gatgoutkouni-creator/Assistance-soudure-PCB/PFE kouni/decoupe laser/Pièce3.DXF

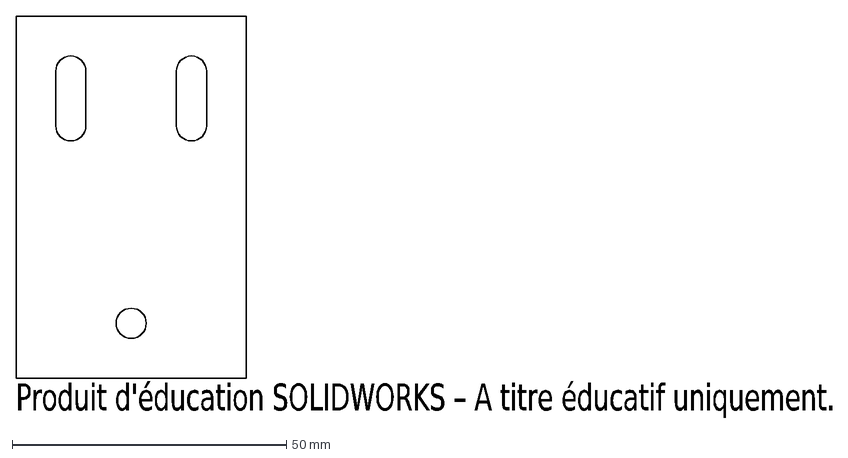
[picture p14: CAD file, 2026-09-05]
PFE kouni/decoupe laser/Pièce3.DXF
Produit d'éducation SOLIDWORKS – A titre éducatif uniquement.
