gatgoutkouni-creator/Assistance-soudure-PCB/PFE kouni/vis.SLDPRT

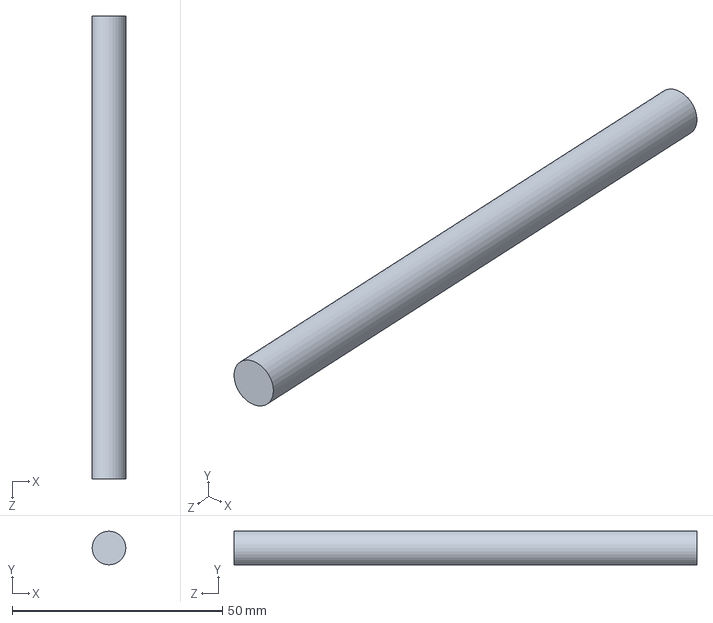
[picture p15: CAD file, 2026-09-05]
PFE kouni/vis.SLDPRT
8.00 x 8.00 x 110.0 mm
