gatgoutkouni-creator/Assistance-soudure-PCB/PFE kouni/decoupe laser/plaque v slot 2.DXF

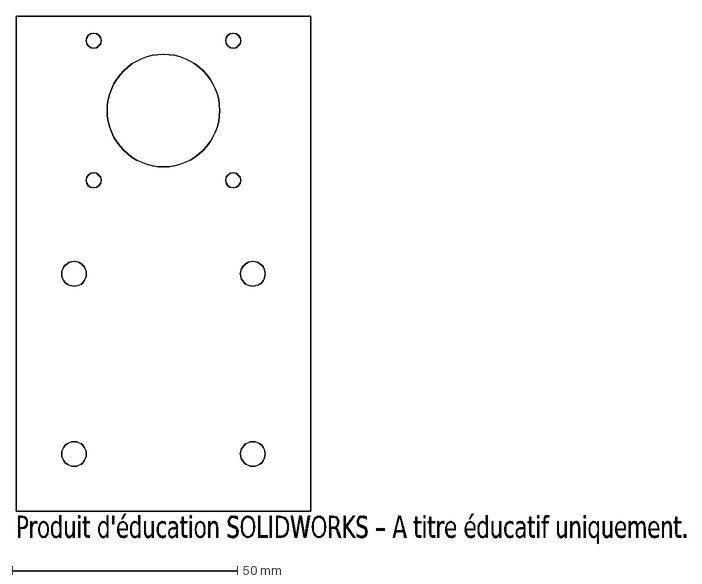
[picture p16: CAD file, 2026-09-05]
PFE kouni/decoupe laser/plaque v slot 2.DXF
Produit d'éducation SOLIDWORKS – A titre éducatif uniquement.
