gatgoutkouni-creator/Assistance-soudure-PCB/PFE kouni/fer/fer partie 2.SLDPRT

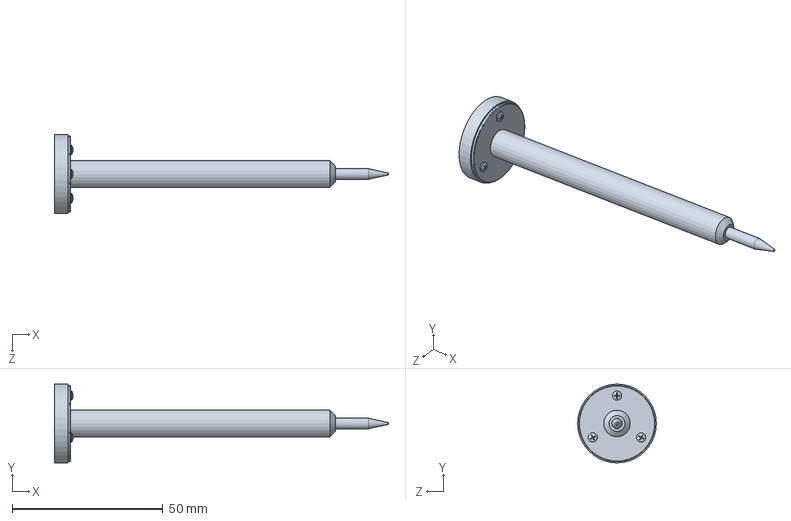
[picture p17: CAD file, 2026-09-05]
PFE kouni/fer/fer partie 2.SLDPRT
110.9 x 26.2 x 26.2 mm
