gatgoutkouni-creator/Assistance-soudure-PCB/PFE kouni/impression/Pièce3.STL

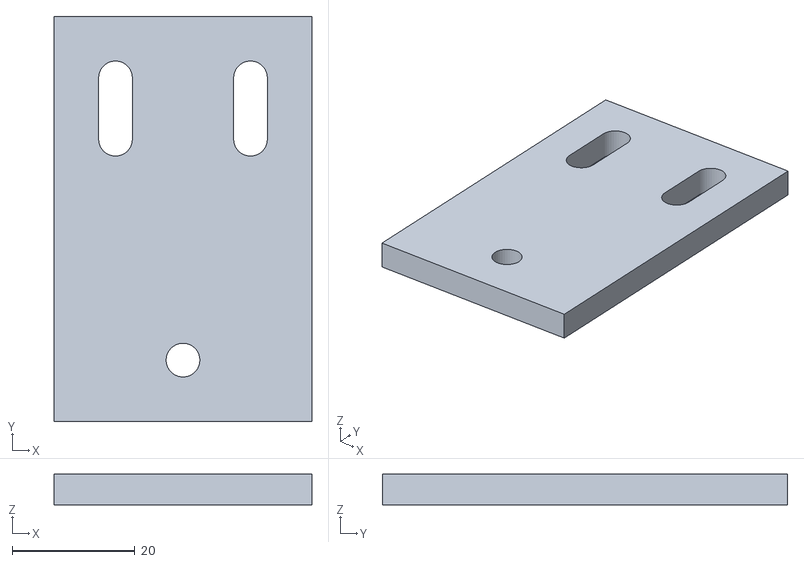
[picture p18: CAD file, 2026-09-05]
PFE kouni/impression/Pièce3.STL
42.0 x 66.0 x 5.00
