gatgoutkouni-creator/Assistance-soudure-PCB/PFE kouni/KOUNIII PIEECE 1 YTB.SLDPRT

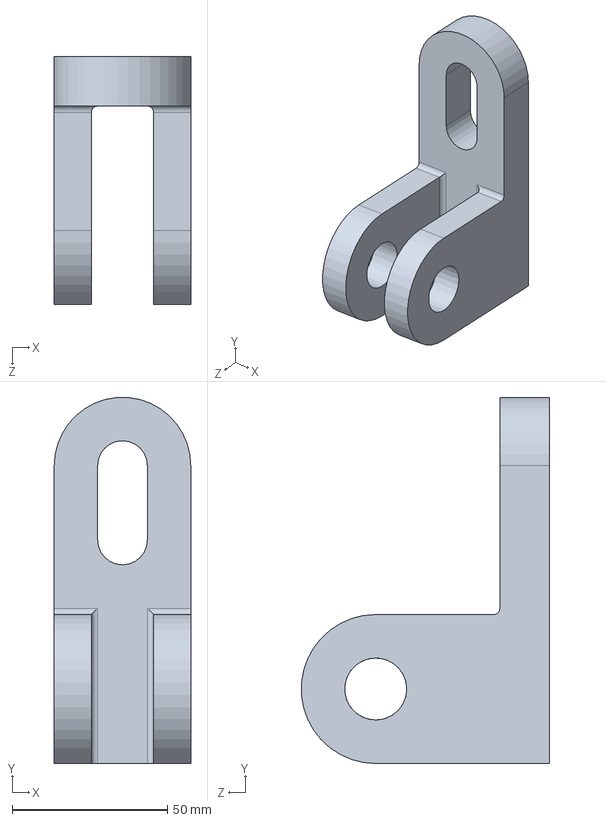
[picture p19: CAD file, 2026-09-05]
PFE kouni/KOUNIII PIEECE 1 YTB.SLDPRT
44.0 x 117.9 x 79.9 mm
