gatgoutkouni-creator/Assistance-soudure-PCB/PFE kouni/palier.SLDPRT

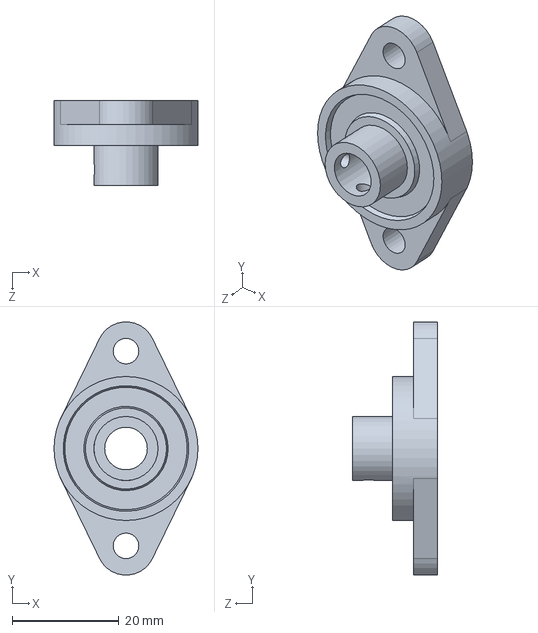
[picture p20: CAD file, 2026-09-05]
PFE kouni/palier.SLDPRT
27.0 x 47.4 x 16.0 mm
