gatgoutkouni-creator/Assistance-soudure-PCB/PFE kouni/courroie.SLDPRT

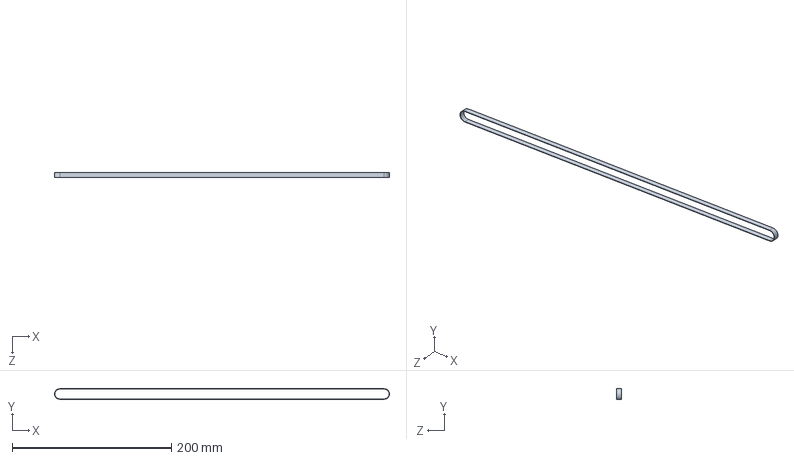
[picture p21: CAD file, 2026-09-05]
PFE kouni/courroie.SLDPRT
420.2 x 13.2 x 6.00 mm
