gatgoutkouni-creator/Assistance-soudure-PCB/PFE kouni/GHLIDH 2.SLDPRT

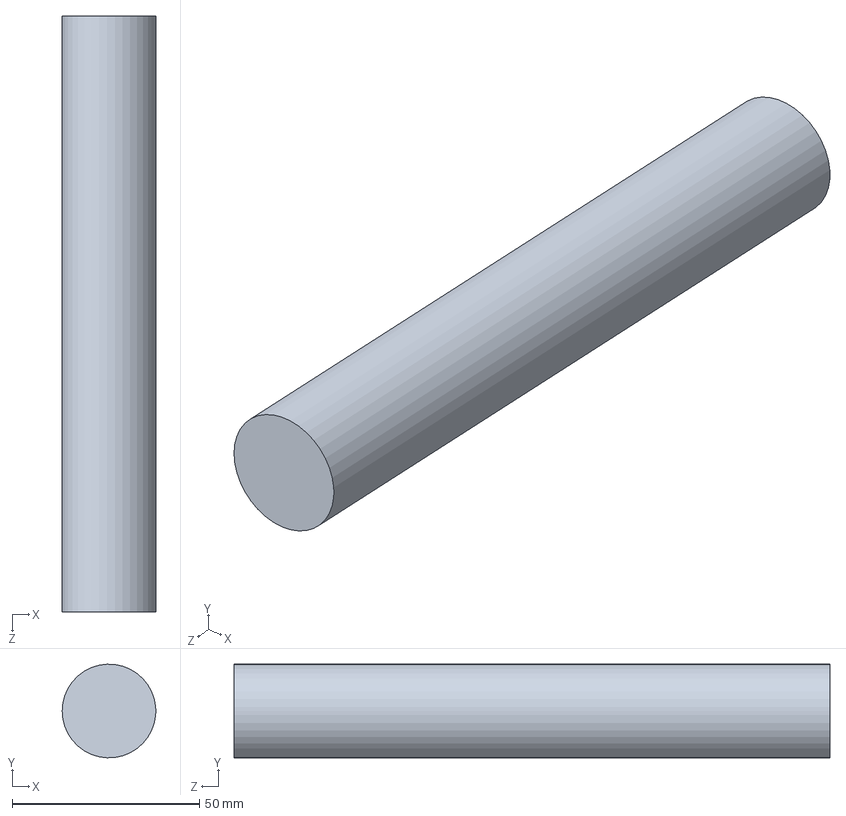
[picture p22: CAD file, 2026-09-05]
PFE kouni/GHLIDH 2.SLDPRT
25.0 x 25.0 x 159.0 mm
