gatgoutkouni-creator/Assistance-soudure-PCB/PFE kouni/plaque axe z.SLDPRT

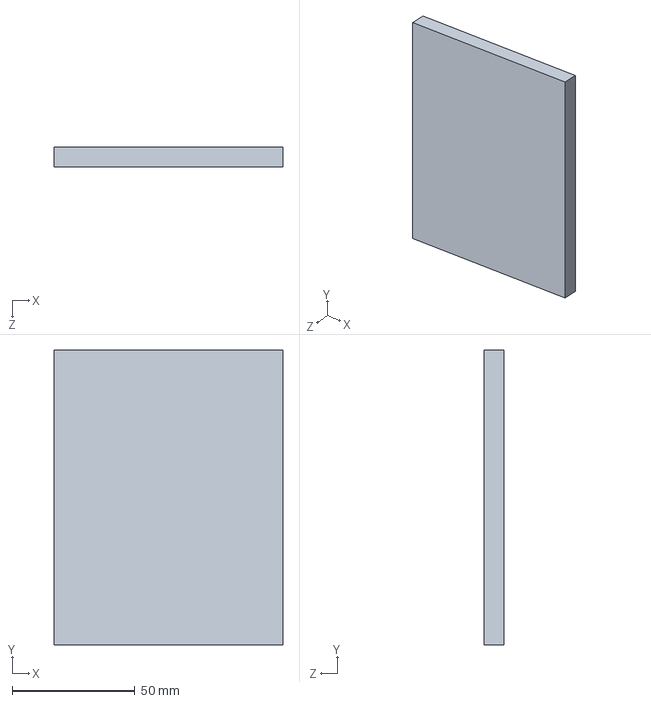
[picture p23: CAD file, 2026-09-05]
PFE kouni/plaque axe z.SLDPRT
93.0 x 120.0 x 8.00 mm
