gatgoutkouni-creator/Assistance-soudure-PCB/PFE kouni/Pièce2 YTB.SLDPRT

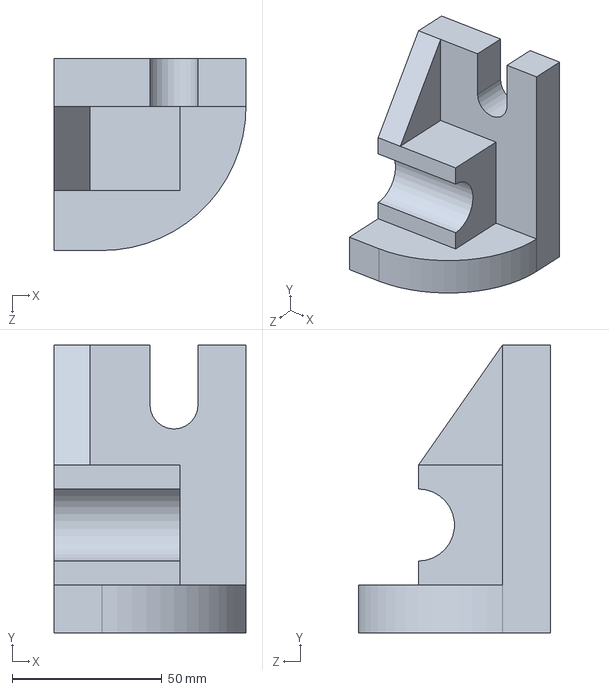
[picture p24: CAD file, 2026-09-05]
PFE kouni/Pièce2 YTB.SLDPRT
64.0 x 96.0 x 64.0 mm
