gatgoutkouni-creator/Assistance-soudure-PCB/PFE kouni/guidage z.SLDPRT

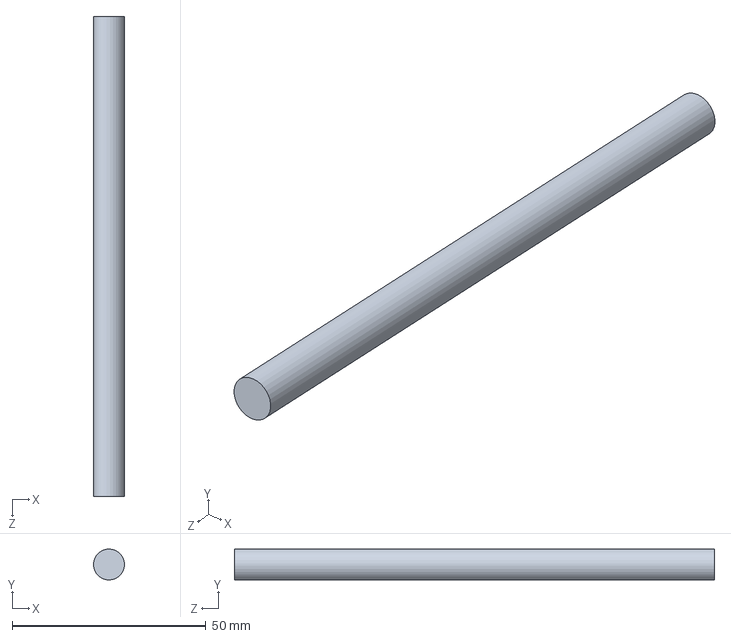
[picture p25: CAD file, 2026-09-05]
PFE kouni/guidage z.SLDPRT
8.00 x 7.99 x 124.0 mm
