gatgoutkouni-creator/Assistance-soudure-PCB/PFE kouni/v-slot X2.SLDPRT

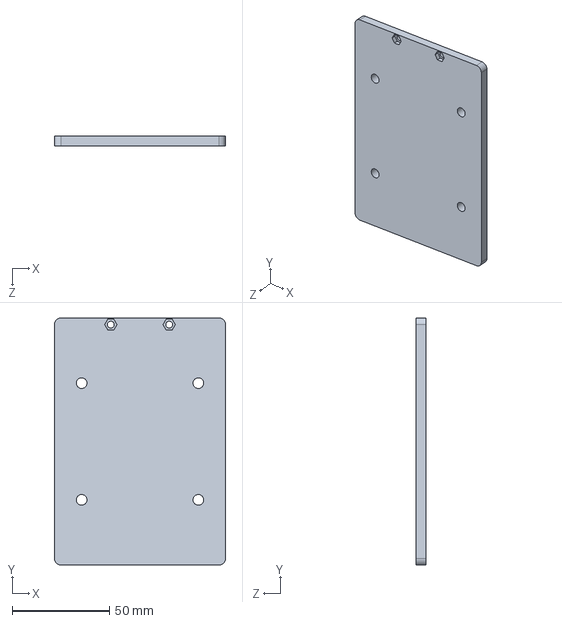
[picture p26: CAD file, 2026-09-05]
PFE kouni/v-slot X2.SLDPRT
88.0 x 127.0 x 5.00 mm
