gatgoutkouni-creator/Assistance-soudure-PCB/PFE kouni/42SHD0034-20B.SLDPRT

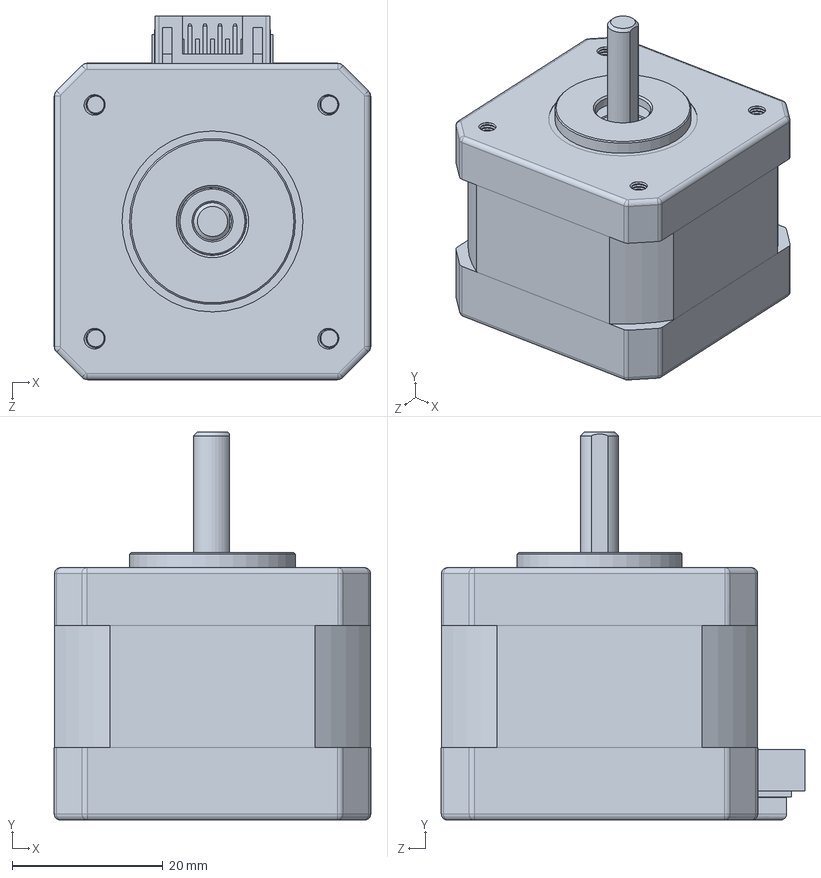
[picture p27: CAD file, 2026-09-05]
PFE kouni/42SHD0034-20B.SLDPRT
42.0 x 51.5 x 48.2 mm
