gatgoutkouni-creator/Assistance-soudure-PCB/PFE kouni/3030 ALUMINIUM EXTRUSION.SLDPRT

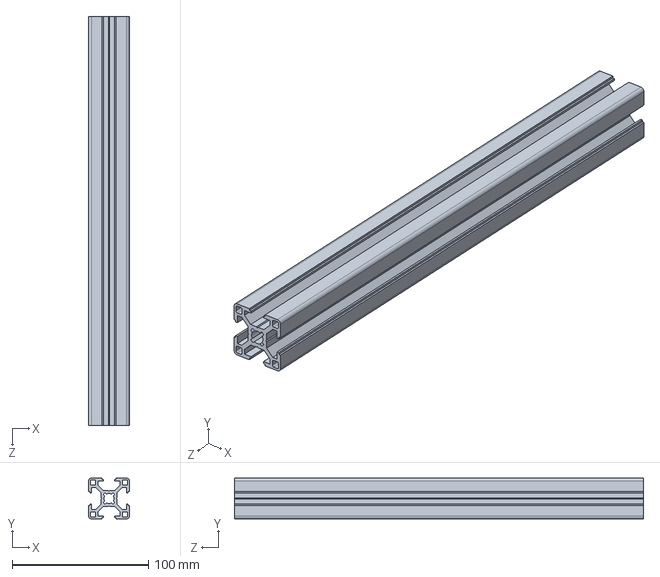
[picture p28: CAD file, 2026-09-05]
PFE kouni/3030 ALUMINIUM EXTRUSION.SLDPRT
30.0 x 30.0 x 300.0 mm
