gatgoutkouni-creator/Assistance-soudure-PCB/PFE kouni/roulement lineaire.SLDPRT

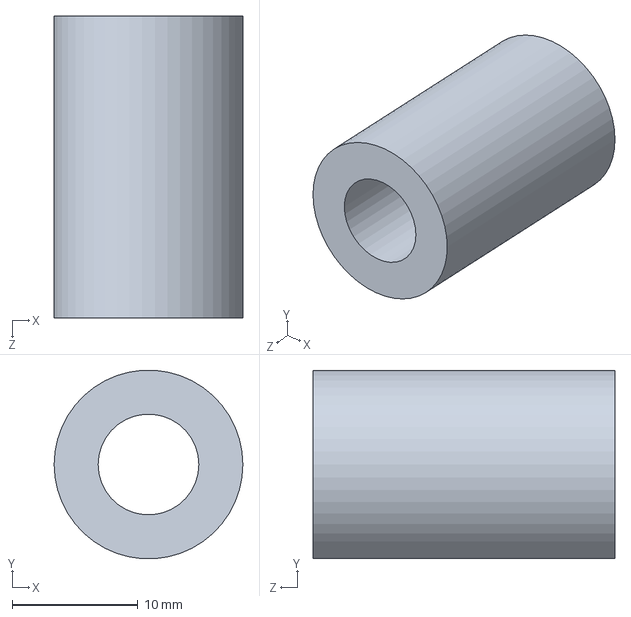
[picture p29: CAD file, 2026-09-05]
PFE kouni/roulement lineaire.SLDPRT
15.0 x 15.0 x 24.0 mm
