gatgoutkouni-creator/Assistance-soudure-PCB/PFE kouni/obs courroie.SLDPRT

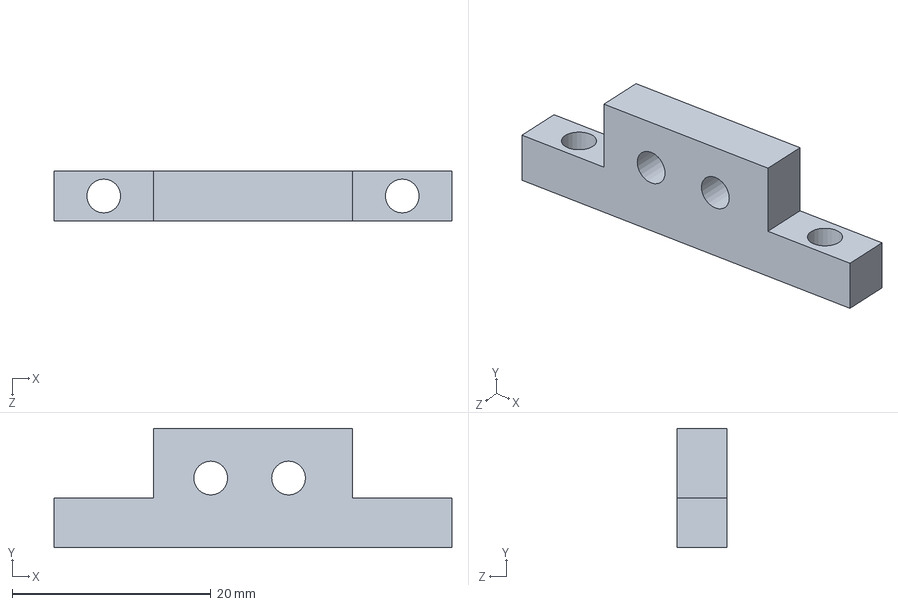
[picture p30: CAD file, 2026-09-05]
PFE kouni/obs courroie.SLDPRT
40.0 x 12.0 x 5.00 mm
