gatgoutkouni-creator/Assistance-soudure-PCB/PFE kouni/cphg19-5-8_01.SLDPRT

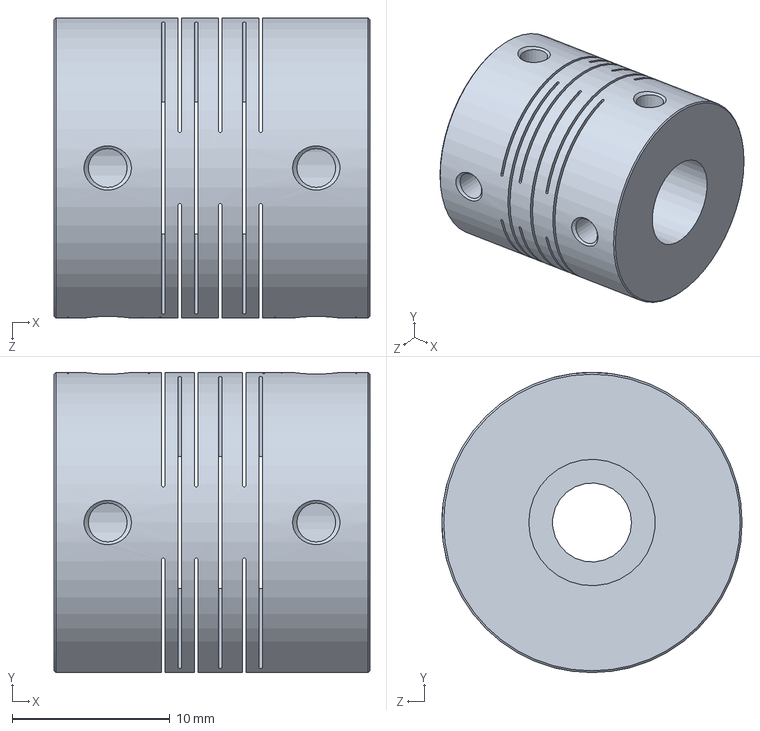
[picture p31: CAD file, 2026-09-05]
PFE kouni/cphg19-5-8_01.SLDPRT
20.0 x 19.0 x 19.0 mm
