gatgoutkouni-creator/Assistance-soudure-PCB/PFE kouni/GHLIDH.SLDPRT

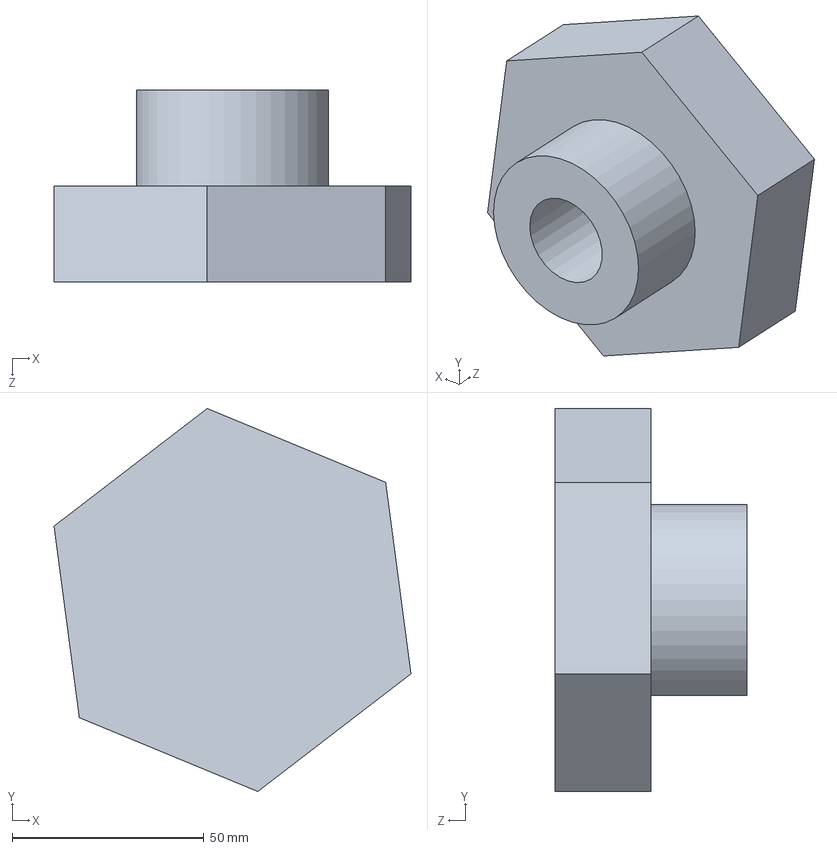
[picture p32: CAD file, 2026-09-05]
PFE kouni/GHLIDH.SLDPRT
93.2 x 100.0 x 50.0 mm
