gatgoutkouni-creator/Assistance-soudure-PCB/PFE kouni/pas a pas etain.SLDPRT

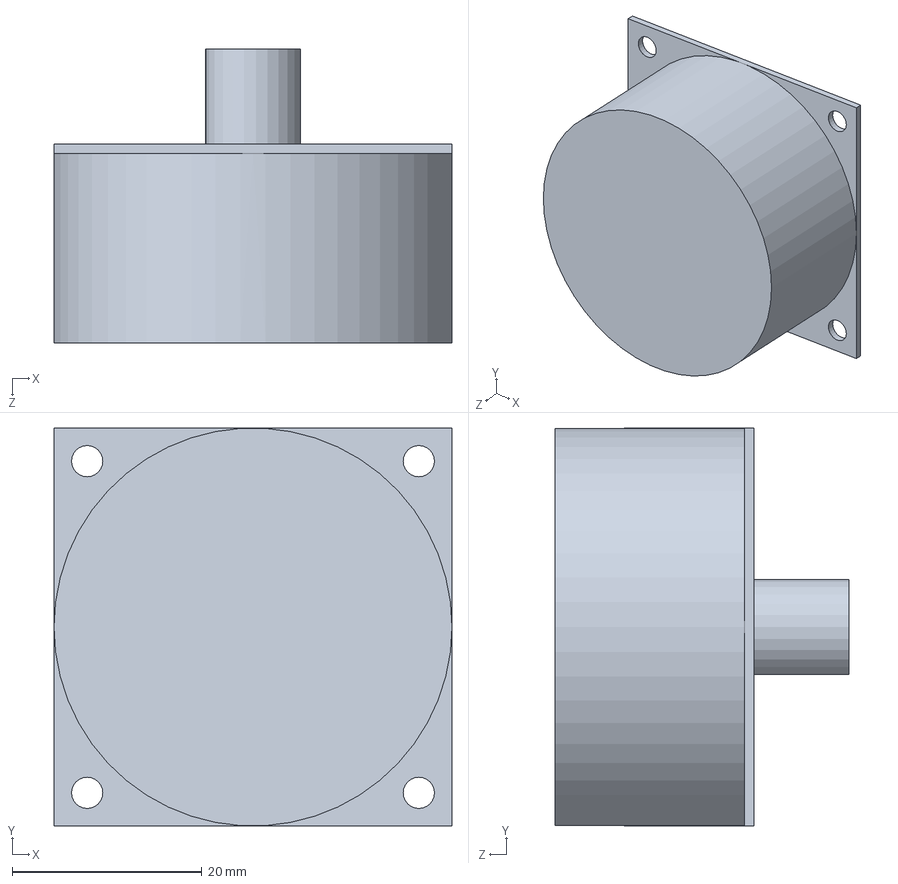
[picture p33: CAD file, 2026-09-05]
PFE kouni/pas a pas etain.SLDPRT
42.0 x 42.0 x 31.0 mm
