gatgoutkouni-creator/Assistance-soudure-PCB/PFE kouni/table.SLDPRT

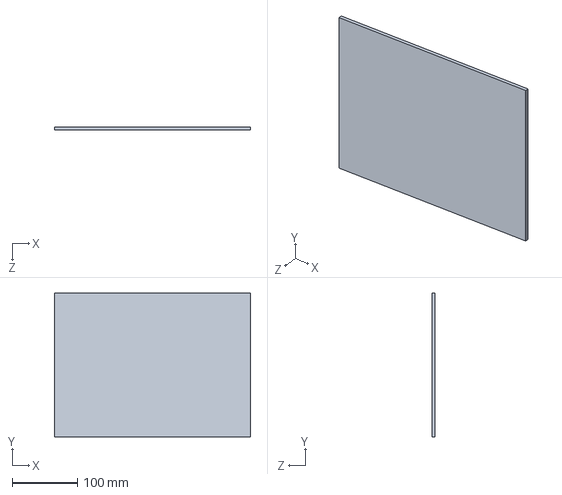
[picture p34: CAD file, 2026-09-05]
PFE kouni/table.SLDPRT
300.0 x 220.0 x 5.00 mm
