gatgoutkouni-creator/Assistance-soudure-PCB/PFE kouni/support etain.SLDPRT

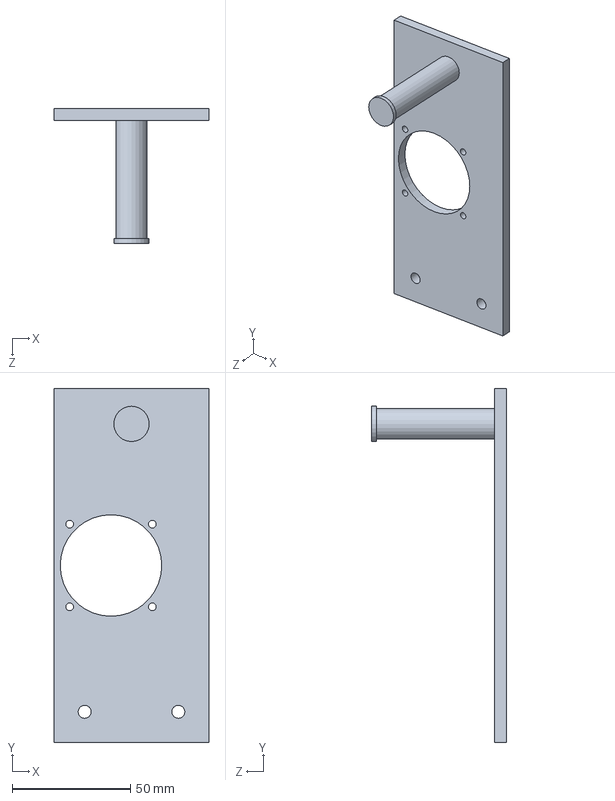
[picture p35: CAD file, 2026-09-05]
PFE kouni/support etain.SLDPRT
65.5 x 150.0 x 57.0 mm
