gatgoutkouni-creator/Assistance-soudure-PCB/PFE kouni/GT2 x 6mm Pully 5mm Bore syncro.SLDPRT

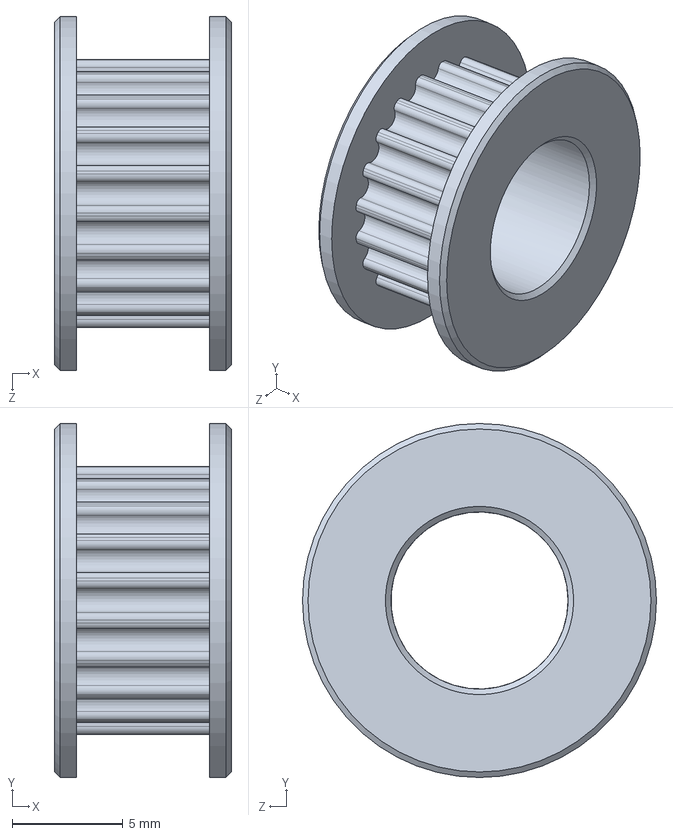
[picture p36: CAD file, 2026-09-05]
PFE kouni/GT2 x 6mm Pully 5mm Bore syncro.SLDPRT
8.00 x 16.0 x 16.0 mm
