gatgoutkouni-creator/Assistance-soudure-PCB/PFE kouni/Aluminum Profile 2040.SLDPRT

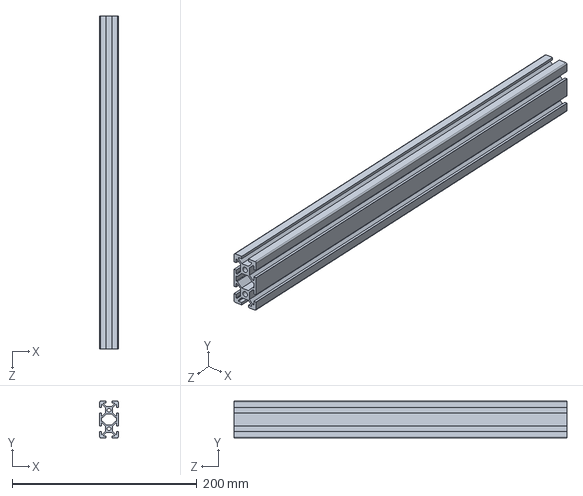
[picture p37: CAD file, 2026-09-05]
PFE kouni/Aluminum Profile 2040.SLDPRT
20.0 x 40.0 x 360.0 mm
