gatgoutkouni-creator/Assistance-soudure-PCB/PFE kouni/support ecrou.SLDPRT

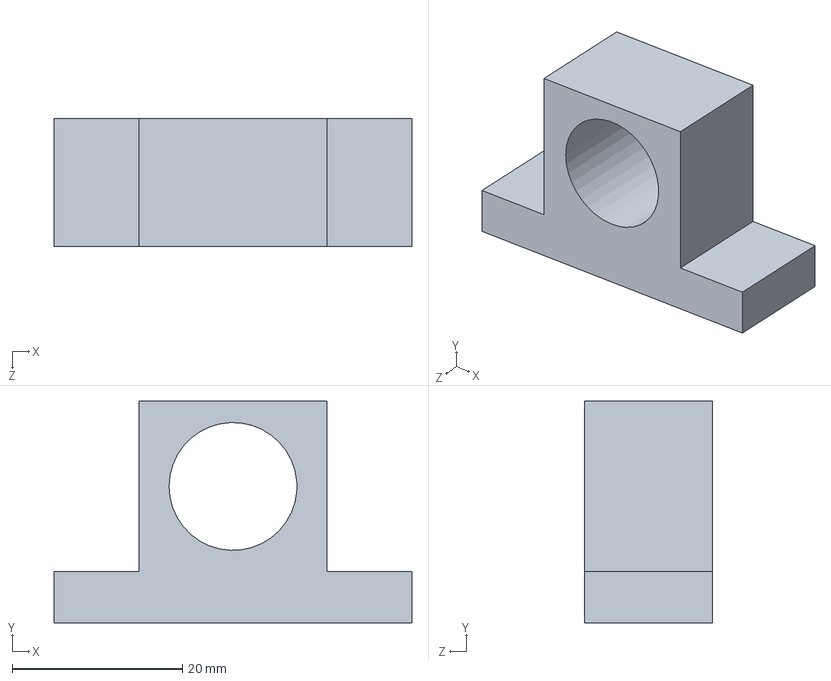
[picture p38: CAD file, 2026-09-05]
PFE kouni/support ecrou.SLDPRT
42.0 x 26.0 x 15.0 mm
