gatgoutkouni-creator/Assistance-soudure-PCB/PFE kouni/2020 ALUMINIUM EXTRUSION.SLDPRT

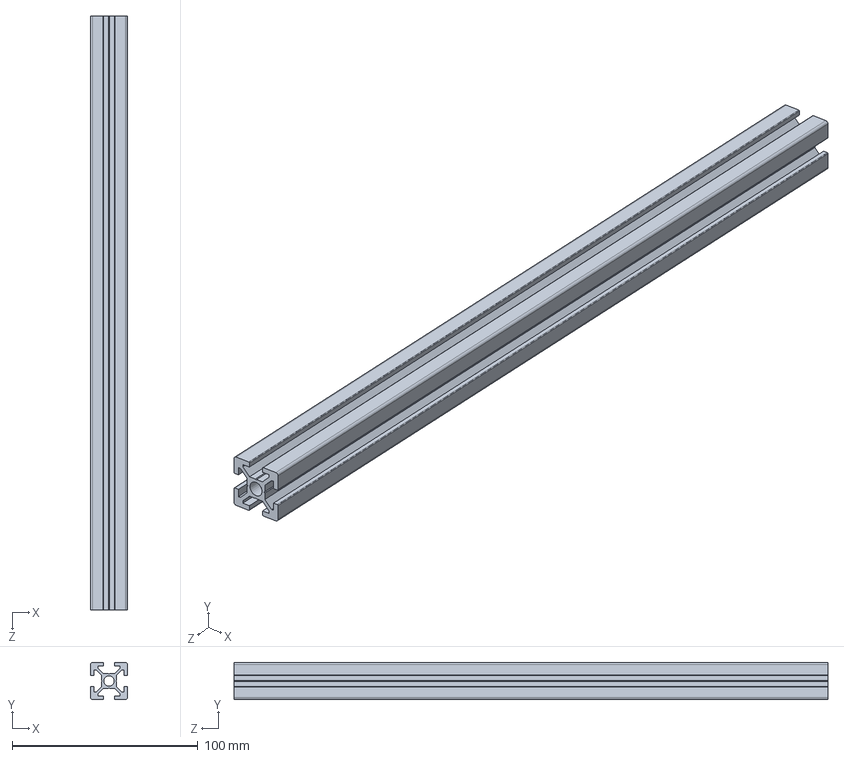
[picture p39: CAD file, 2026-09-05]
PFE kouni/2020 ALUMINIUM EXTRUSION.SLDPRT
20.0 x 20.0 x 320.0 mm
