gatgoutkouni-creator/Assistance-soudure-PCB/PFE kouni/support douille.SLDPRT

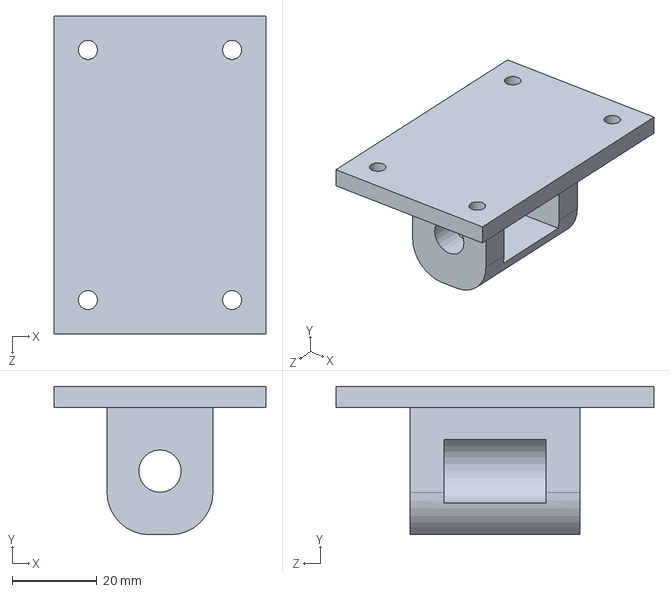
[picture p40: CAD file, 2026-09-05]
PFE kouni/support douille.SLDPRT
50.0 x 35.0 x 75.0 mm
