gatgoutkouni-creator/Assistance-soudure-PCB/PFE kouni/v-slot X.SLDPRT

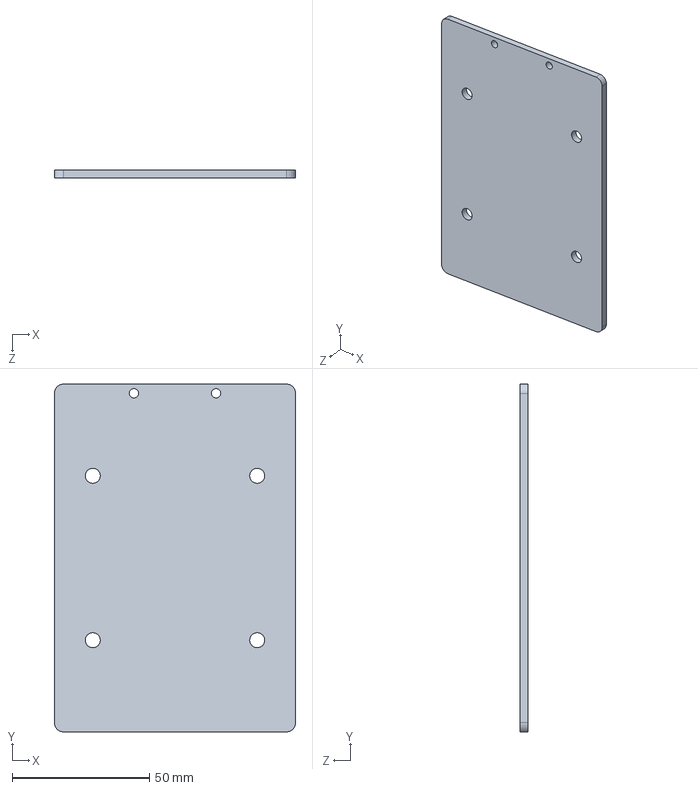
[picture p41: CAD file, 2026-09-05]
PFE kouni/v-slot X.SLDPRT
88.0 x 127.0 x 3.00 mm
