gatgoutkouni-creator/Assistance-soudure-PCB/PFE kouni/Pully GT2-Bore5mm-20Teeth.SLDPRT

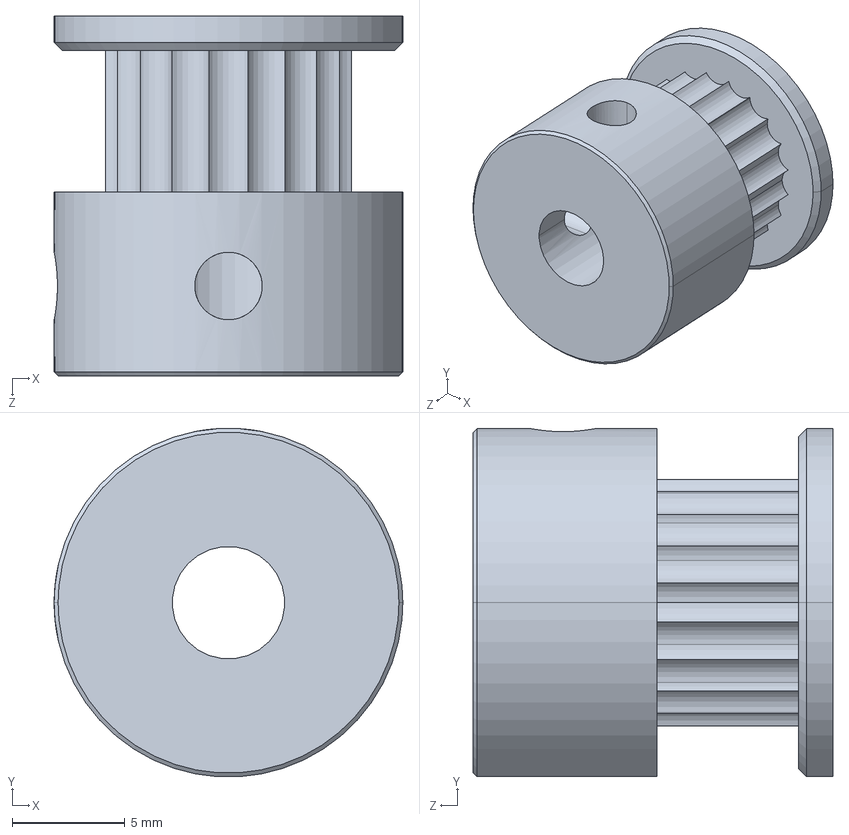
[picture p42: CAD file, 2026-09-05]
PFE kouni/Pully GT2-Bore5mm-20Teeth.SLDPRT
15.5 x 15.5 x 16.0 mm
