gatgoutkouni-creator/Assistance-soudure-PCB/PFE kouni/fixation axe x.SLDPRT

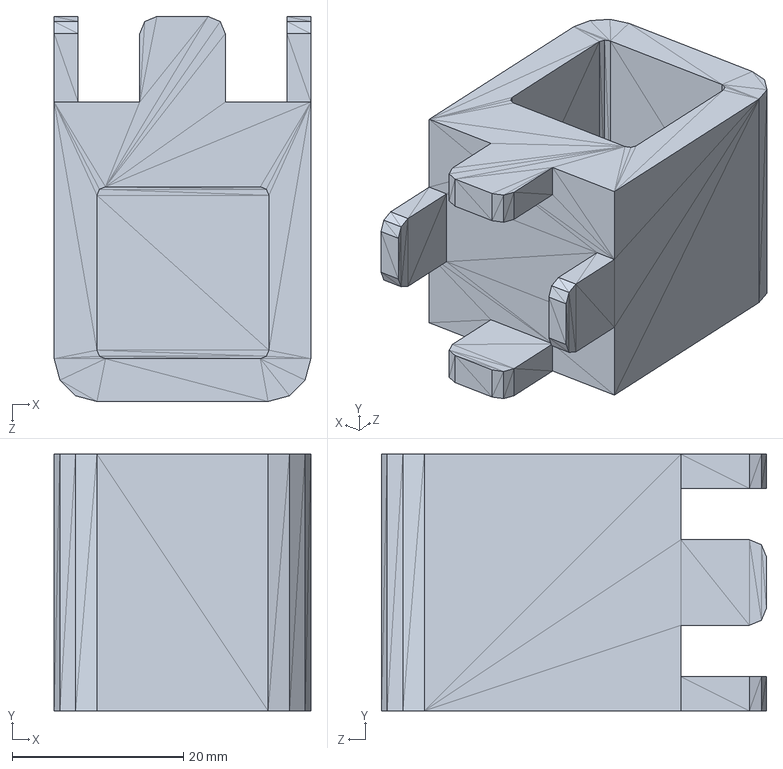
[picture p43: CAD file, 2026-09-05]
PFE kouni/fixation axe x.SLDPRT
30.0 x 30.0 x 45.0 mm
