gatgoutkouni-creator/Assistance-soudure-PCB/PFE kouni/GT2 x 6mm Pully 5mm Bore.SLDPRT

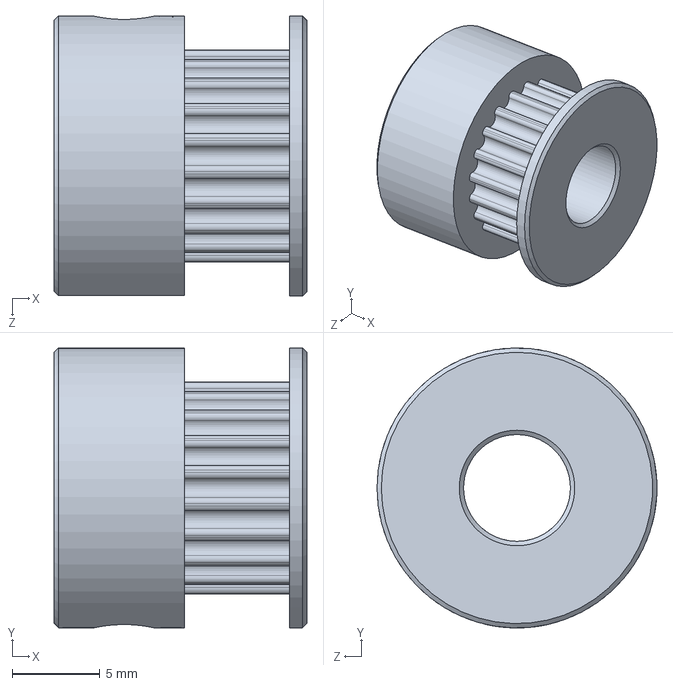
[picture p44: CAD file, 2026-09-05]
PFE kouni/GT2 x 6mm Pully 5mm Bore.SLDPRT
14.4 x 16.0 x 16.0 mm
