gatgoutkouni-creator/Assistance-soudure-PCB/PFE kouni/plaque v slot 2.SLDPRT

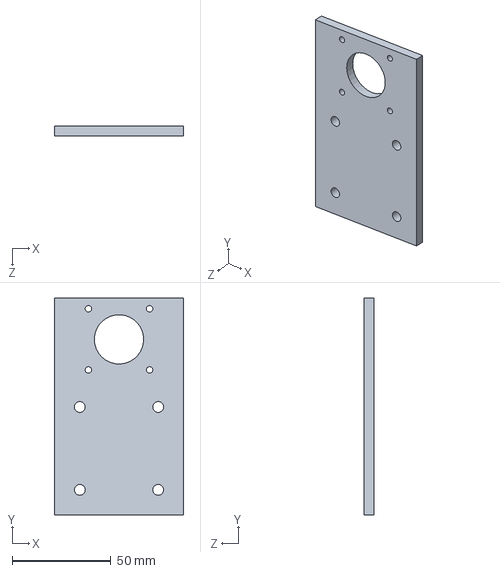
[picture p45: CAD file, 2026-09-05]
PFE kouni/plaque v slot 2.SLDPRT
65.5 x 110.0 x 5.00 mm
