gatgoutkouni-creator/Assistance-soudure-PCB/PFE kouni/plaque v slot.SLDPRT

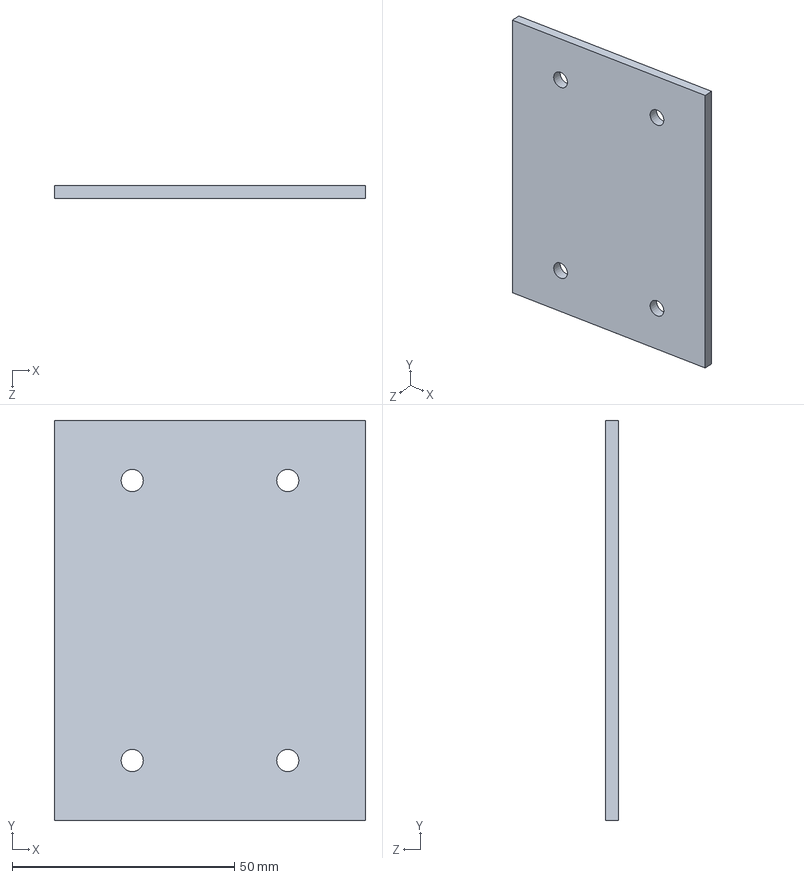
[picture p46: CAD file, 2026-09-05]
PFE kouni/plaque v slot.SLDPRT
70.0 x 90.0 x 3.00 mm
