gatgoutkouni-creator/Assistance-soudure-PCB/PFE kouni/support moteur.SLDPRT

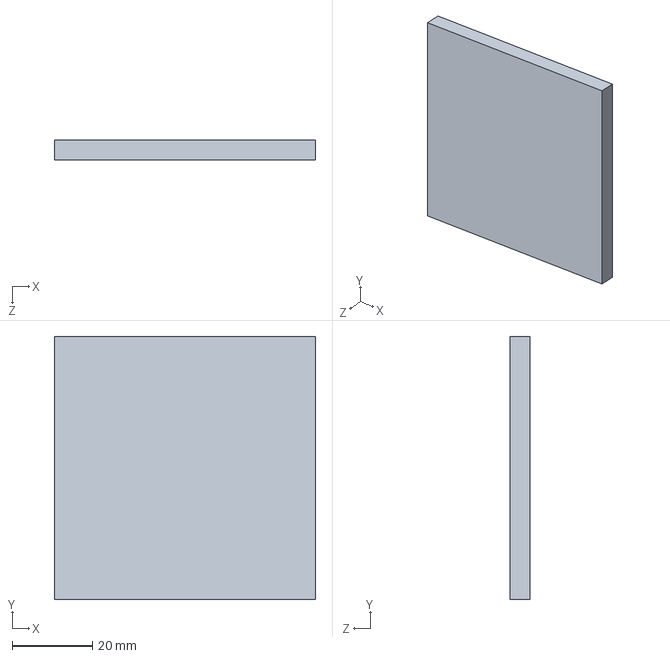
[picture p47: CAD file, 2026-09-05]
PFE kouni/support moteur.SLDPRT
65.0 x 65.5 x 5.00 mm
