gatgoutkouni-creator/Assistance-soudure-PCB/PFE kouni/Pièce5.SLDPRT

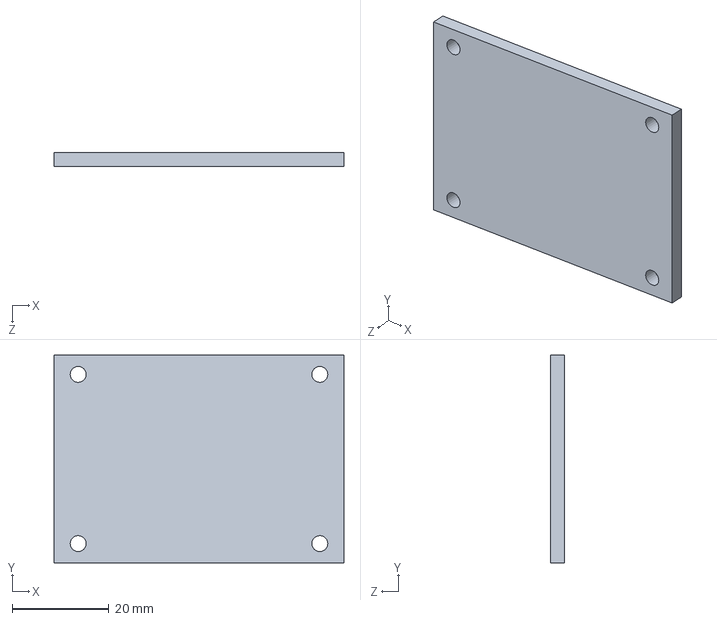
[picture p48: CAD file, 2026-09-05]
PFE kouni/Pièce5.SLDPRT
60.0 x 43.0 x 3.00 mm
