gatgoutkouni-creator/Assistance-soudure-PCB/PFE kouni/SUIVEUR.SLDPRT

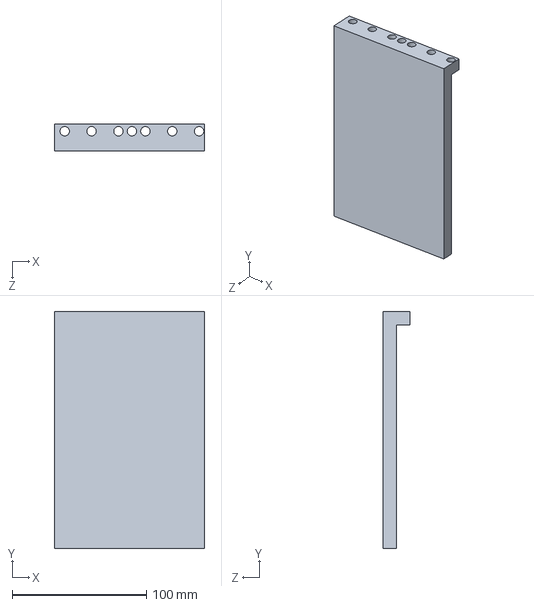
[picture p49: CAD file, 2026-09-05]
PFE kouni/SUIVEUR.SLDPRT
111.9 x 176.3 x 20.0 mm
