gatgoutkouni-creator/Assistance-soudure-PCB/PFE kouni/Pièce24YTB.SLDPRT

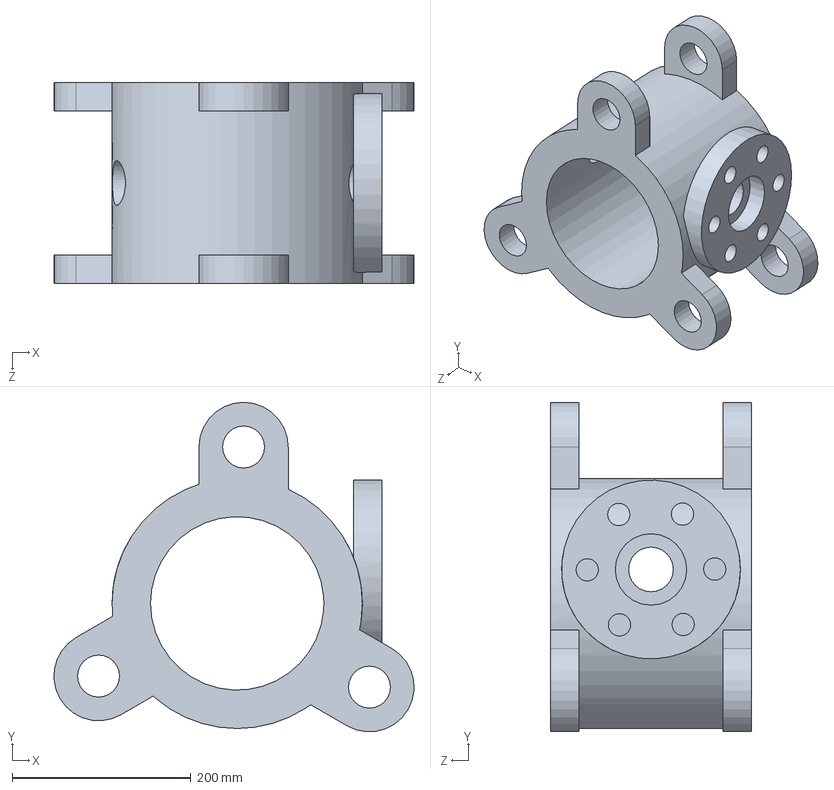
[picture p50: CAD file, 2026-09-05]
PFE kouni/Pièce24YTB.SLDPRT
402.8 x 368.6 x 225.0 mm
