gatgoutkouni-creator/Assistance-soudure-PCB/PFE kouni/cale.SLDPRT

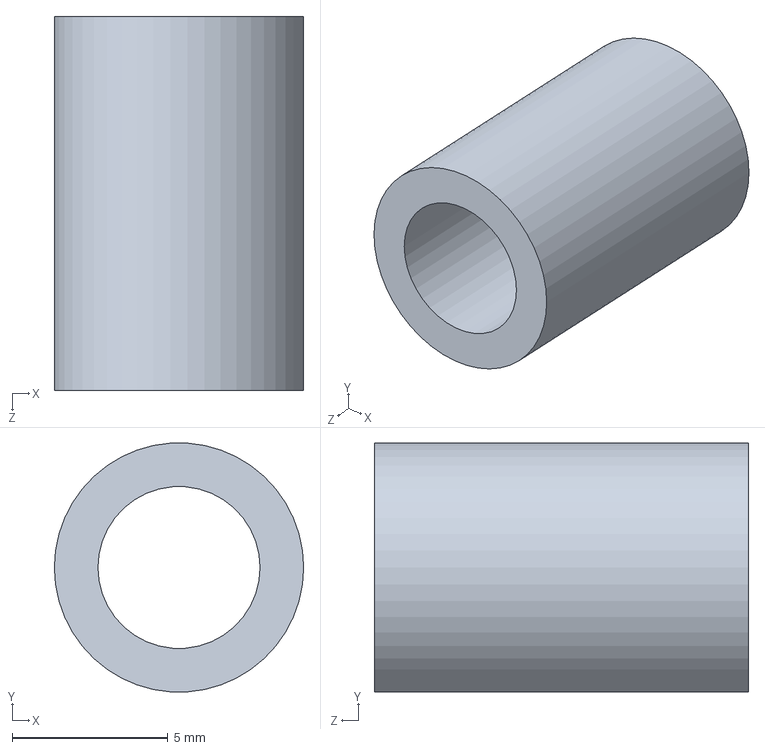
[picture p51: CAD file, 2026-09-05]
PFE kouni/cale.SLDPRT
8.00 x 7.98 x 12.0 mm
