gatgoutkouni-creator/Assistance-soudure-PCB/PFE kouni/plaque z.SLDPRT

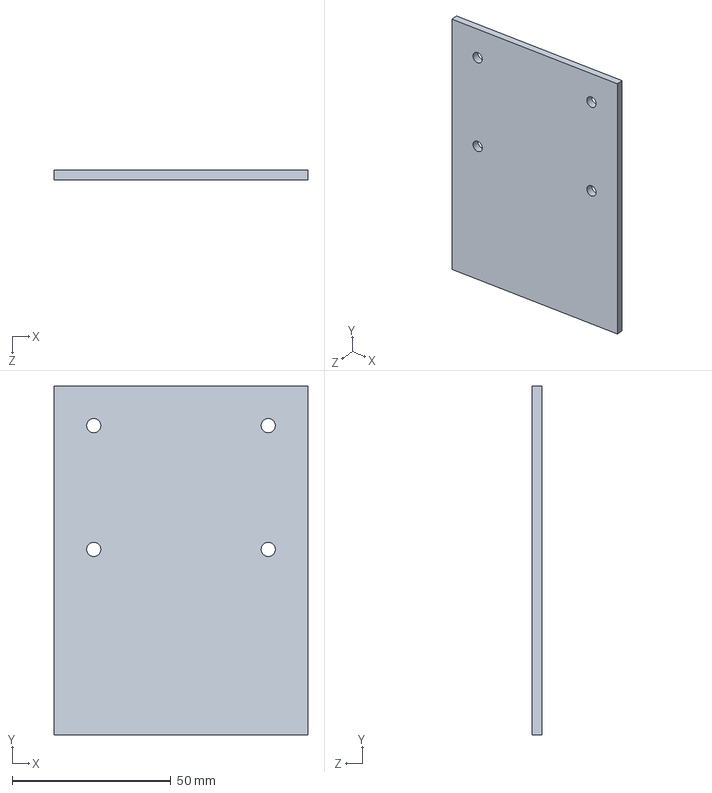
[picture p52: CAD file, 2026-09-05]
PFE kouni/plaque z.SLDPRT
80.0 x 110.0 x 3.00 mm
