gatgoutkouni-creator/Assistance-soudure-PCB/PFE kouni/KP08.SLDASM

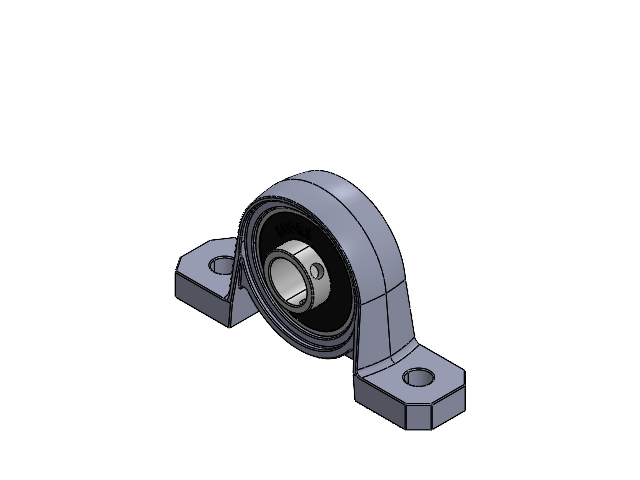
[picture p56: CAD file, 2026-09-05]
PFE kouni/KP08.SLDASM
KP08_1.STEP
608RS.STEP
