gatgoutkouni-creator/Assistance-soudure-PCB/PFE kouni/20mm Gantry Set.SLDASM

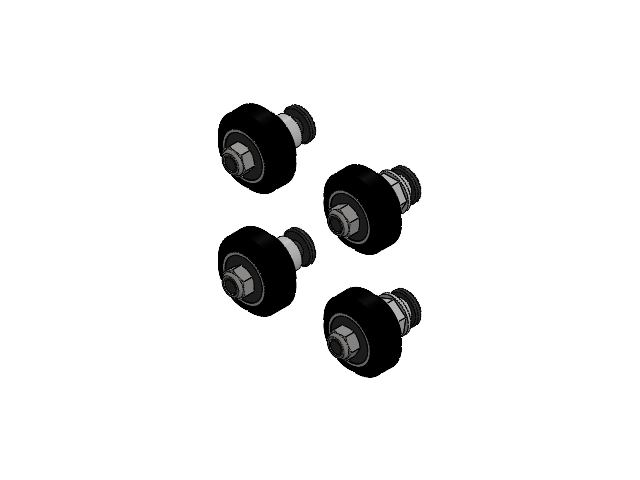
[picture p57: CAD file, 2026-09-05]
PFE kouni/20mm Gantry Set.SLDASM
Solid V-Wheel_2 x 4
Ball Bearing 625 2RS 5x16x5_2 x 8
Eccentric Spacer_1 x 2
1mm 5mm shim_2 x 4
6mm Spacer_1 x 2
M5x25 low profile screw_1 x 4
M5 Nylock_1 x 4
